felixkuebler/HomeAutomation-MotorController/Hardware/Electronics/Render/MotorController_back.png

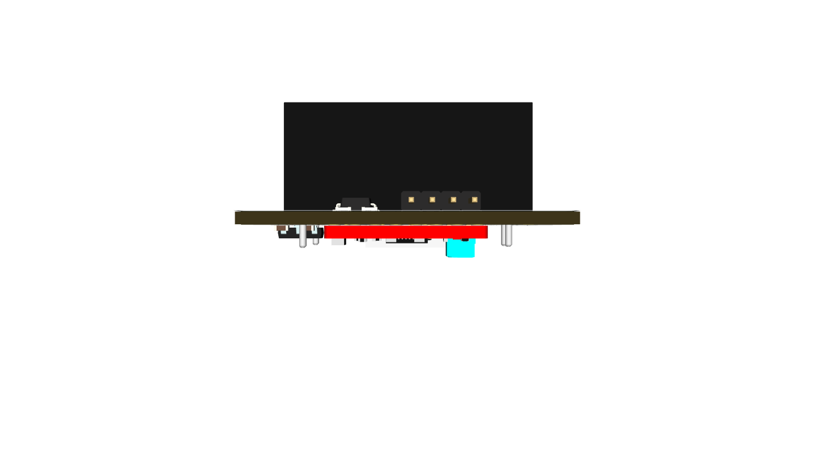
Hardware/Electronics/Render/MotorController_back.png
