felixkuebler/HomeAutomation-MotorController/Software/Source/MotorController/web_interface.h

#ifndef WEB_INTERFACE
#define WEB_INTERFACE


String generateHeader(wifi_obj wifi_info)
{
  String page="";

  page += "<header>" + wifi_info.host_name +" Settings</header>";

  return page;
}

String generateGeneralSettings(wifi_obj wifi_info)
{
  String page = "";
  
  page +="<div id=\"general\">";
    page +="<h1>General Settings</h1>";
    page +="<br>";
    page +="<div>";
      page +="Device Name ";
      page +="<input class=\"text-input\" type=\"text\" id=\"host_name\" value=\"" + wifi_info.host_name + "\">";
    page +="</div>";
    page +="<br>";
    page +="<div>";
      page +="Device Password ";
      page +="<input class=\"text-input\" type=\"text\" id=\"host_pw\" value=\"" + wifi_info.host_pw + "\">";
    page +="</div>";
    page +="<br>";
    page +="<div class=\"info\">Choose a device name to access this website from your local network (http://device-name/). If the device is not able to connect to the network a wifi hotspot with an identical name will be generated.</div>";
    page += "<br>";
    page += "<br>";
    page +="<div>";
      page +="Update Firmware";
      page +="<form class='update-form' method='POST' action='/update' enctype='multipart/form-data'>";
        page +="<input class='file-input' type='file' name='update'>";
        page +="<input class='btn-input' type='submit' value='Update'>";
      page +="</form>";
    page +="</div>";
  page +="</div>";

  return page;
}

String generateWifiSettings(wifi_obj wifi_info)
{
  String page ="";

  page += "<div class=\"hidden\" id=\"wifi\">";
    page += "<h1>WiFi Settings</h1>";
    page += "<br>";
    page += "<div>";
      page += "Network Name "; 
      page += "<select class=\"select-input\" id=\"wifi_ssid\">";
        page += "<option value=\"" + wifi_info.wifi_ssid + "\">" + wifi_info.wifi_ssid + "</option>";

        int wifiCount = WiFi.scanNetworks();
        for(int i=0; i< wifiCount; i++)
        {
          page += "<option value=\"" + WiFi.SSID(i) + "\">" + WiFi.SSID(i) + "</option>";
        }
      page += "</select>"; 
    page += "</div>";
    page += "<br>";
    page += "<div>";
      page += "Network Password ";
      page += "<input class=\"text-input\" type=\"text\" id=\"wifi_pw\" value=\"" + wifi_info.wifi_pw + "\">";
    page += "</div>";
    page += "<br>";
    page += "<div class=\"info\">Select a Network for this device to connect to. The selected Network must be password protected!</div>";
  page += "</div>";
  
  return page;
}


String generateMQTTSettings(wifi_obj wifi_info, motor_obj motor_info)
{
  String page = "";
  
  page += "<div class=\"hidden\" id=\"mqtt\">";
    page += "<h1>MQTT Settings</h1>";
    page += "<br>";
    page += "<div>";
      page += "Broker IP ";
      page += "<input class=\"text-input\" type=\"text\" id=\"mqtt_broker\" value=\"" + wifi_info.mqtt_broker + "\">";
    page += "</div>";
    page += "<br>";
    page +="<div class=\"info\">Enter the local IP of your MQTT broker (e.g. Mosquitto on a Raspbarry Pi).</div>";
    page += "<br>";
    page += "<div>";
      page += "<br>";        
      page += "<div>";
        page += "Motor Topic ";
        page += "<input class=\"text-input\" type=\"text\" id=\"motor_topic\" value=\"" + motor_info.topic + "\">";
      page += "</div>";
      page += "<br>";
      page += "<div>";
        page += "Motor Range ";
        page += "<input class=\"text-input\" type=\"text\" id=\"motor_range_extern\" value=\"" + motor_info.range_extern + "\">";
      page += "</div>";
      page += "<br>";
      page += "<div>";
        page += "<button class=\"btn-input btn-commands\" onclick=\"calibrateMotor()\">Motor Calibration</button>";      
      page += "</div>";
    page += "</div>";  
  page += "</div>";

  return page;
}

String generateOpenhabScript()
{
  String switch_id;
  String switch_name;

  String switch_mqtt_topic;

  String switch_command_on;
  String switch_command_off;
  String switch_command_toggle;

  String for_sitemap = "";
  for_sitemap += "Switch item=" + switch_id;

  String for_items = "";
  for_items += "Switch " + switch_id + "\"" + switch_name + "\"";
  for_items += "{mqtt=\"";
  for_items += ">[broker:" + switch_mqtt_topic + ":command:ON:" + switch_command_on + "],";
  for_items += ">[broker:" + switch_mqtt_topic + ":command:OFF:" + switch_command_off + "]";
  for_items += "\"}\n";
  for_items += "String mqttMessage_" + switch_id + " {mqtt=\"<[broker:" + switch_mqtt_topic + ":state:default]\"}";

  String for_rules = "";
  for_rules += "rule \"mqttMessage_" + switch_id + "_changed\n";
  for_rules += "when\n";
  for_rules += "\tItem mqttMessage_" + switch_id + " changed\n";
  for_rules += "then\n";
  for_rules += "\tif(mqttMessage_" + switch_id + ".state.toString.contains(\"" + switch_command_off + "\"))\n";
  for_rules += "\t{\n";
  for_rules += "\t\t" + switch_id + ".postUpdate(OFF)\n";
  for_rules += "\t}\n";
  for_rules += "\telse if(mqttMessage_" + switch_id + ".state.toString.contains(\"" + switch_command_on + "\"))\n";
  for_rules += "\t{\n";
  for_rules += "\t\t" + switch_id + ".postUpdate(ON)\n";
  for_rules += "\t}\n";
  for_rules += "\telse if(mqttMessage_" + switch_id + ".state.toString.contains(\"" + switch_command_toggle + "\"))\n";
  for_rules += "\t{\n";
  for_rules += "\t\t" + switch_id + ".postUpdate(if(" + switch_id + ".state == ON) OFF else ON)\n";
  for_rules += "\t\tmqttMessage_" + switch_id + ".postUpdate(\"\")\n";
  for_rules += "\t}\n";
  for_rules += "end";

  return "";
}

String generateScript()
{
  String script ="";
  
  script += "<script>";
    script += "function handleSettings(element){"; 
      script += "var setting_buttons= document.getElementsByClassName(\"btn-settings\");";
      script += "for (var i = 0; i < setting_buttons.length; ++i){";
        script += "var setting_button = setting_buttons[i]; ";
        script += "var setting_frame= document.getElementById(setting_button.getAttribute(\"for\"));";
        script += "setting_button.style.borderWidth= \"1px\";";
        script += "setting_button.style.background = \"rgba(120,120,120,0.95)\";";
        script += "setting_button.classList.remove(\"dontHover\");";
        script += "setting_frame.style.display = \"none\";";
      script += "}";
      script += "var setting_frame = document.getElementById(element.getAttribute(\"for\")); ";
      script += "setting_frame.style.display = \"block\";";
      script += "element.style.borderWidth = \"0\";";
      script += "element.style.background = \"rgba(180,180,180,0.95)\";";
      script += "element.classList.add(\"dontHover\");";
    script += "}";

     script += "function handleOptions(element){"; 
      script += "var setting_buttons= document.getElementsByClassName(\"btn-options\");";
      script += "for (var i = 0; i < setting_buttons.length; ++i){";
        script += "var setting_button = setting_buttons[i]; ";
        script += "var setting_frame= document.getElementById(setting_button.getAttribute(\"for\"));";
        script += "setting_button.style.background = \"rgba(120,120,120,0.95)\";";
        script += "setting_button.classList.remove(\"dontHover\");";
        script += "setting_frame.style.display = \"none\";";
      script += "}";
      script += "var setting_frame = document.getElementById(element.getAttribute(\"for\")); ";
      script += "setting_frame.style.display = \"block\";";
      script += "element.style.background = \"rgba(180,180,180,0.95)\";";
      script += "element.classList.add(\"dontHover\");";
    script += "}";

    script += "function sendSettings(){";
      script += "var msg = \"?\";";
      script += "var selects = document.getElementsByTagName(\"select\");";
      script += "for (var i = 0; i < selects.length; ++i){";
        script += "var id = selects[i].getAttribute(\"id\");";
        script += "var value = selects[i].value;";
        script += "msg+= id + \"=\" + value + \"&\";";
      script += "}";
      script += "var inputs = document.getElementsByTagName(\"input\");";
      script += "for (var i = 0; i < inputs.length; ++i){";
        script += "var id = inputs[i].getAttribute(\"id\");";
        script += "var value = inputs[i].value;";
        script += "msg+= id + \"=\" + value + \"&\";";
      script += "}";
      script += "msg+= \"save_settings=true\";";
      script += "if(confirm(\"The system is going to reboot after the settings are saved. Do You want to continue?\"))";
      script += "{";
        script += "var xhttp = new XMLHttpRequest();";
        script += "xhttp.onreadystatechange = function(){";
          script += "if (this.readyState == 4 && this.status == 200){}";
        script += "};";
        script += "xhttp.open(\"GET\", msg, true);";
        script += "xhttp.send();";
      script += "}";
    script += "}";

    script += "function calibrateMotor(){";
      script += "var xhttp = new XMLHttpRequest();";
      script += "xhttp.onreadystatechange = function(){";
        script += "if (this.readyState == 4 && this.status == 200){}";
      script += "};";
      script += "xhttp.open(\"GET\", \"?motor_calibration=true\", true);";
      script += "xhttp.send();";
    script += "}";
    
    script += "function sendReset(){";
      script += "if(confirm(\"The system is going to roboot after settings are reset to default. Do You want to continue?\"))";
      script += "{";
        script += "var xhttp = new XMLHttpRequest();";
        script += "xhttp.onreadystatechange = function(){";
          script += "if (this.readyState == 4 && this.status == 200){}";
        script += "};";
        script += "xhttp.open(\"GET\", \"?reset_settings=true\", true);";
        script += "xhttp.send();";
      script += "}";
    script += "}";

  script += "</script>";

  return script;
}

String generateCSS()
{
  String css = "";
  
  css += "<style>";
    css += "header {width:100vw; height:25vh; margin:0; padding:0; text-align:center; display: table-cell; vertical-align:middle; font-family:Verdana; font-weight:100; font-size:11vh; background:rgba(180,180,180,0.7)}";
    css += "h1 {margin:0; padding:0; font-family:Verdana; font-weight:100; font-size:6vh}";
    css += "button:focus {outline:0}";
    css += ".main-frame {width:100vw; height:75vh; margin:0; padding:0; overflow:hidden}";
    css += ".left-frame {width:20vw; height:75vh; float:left; margin:0; padding:0; text-align:center; position:relative; font-family:Verdana; font-weight:100; font-size:4vh}";
    css += ".right-frame {width:80vw; height:75vh; float:right; margin:0; padding:0; text-align:center; position:relative; font-family:Verdana; font-weight:100; font-size:3vh; background:rgba(180,180,180,0.95)}";
    css += ".scrollable {overflow:scroll; width:80vw; height:55vh; position:absolute; bottom:0}";
    css += ".spaceholder {width:20vw; height:31.1vh; margin:0; margin-top:30vh; padding:0; text-align:center; font-family:Verdana; font-weight:100; font-size:3vh; background:rgba(120,120,120,0.95)}";
    css += ".info {width:40vw; margin-left: 20vw; font-family:Verdana; font-weight:100; font-size:1.8vh}";
    css += ".hidden {display:none}";
    css += ".btn {background:rgba(120,120,120,0.95); width:20vw; border:none; text-align:center; text-decoration:none; cursor:pointer; margin:0; padding:0; font-family:Verdana; font-weight:100; border-style: solid; border-color:rgba(110,110,110,0.95); border-width:1px;}";
    css += ".btn:not(.dontHover):hover {background:rgba(100,100,100,0.95) !important}";
    css += ".selected {background:rgba(180,180,180,0.95); border-width:1;}";
    css += ".selected-noborder {background:rgba(180,180,180,0.95); border-width:0;}";
    css += ".btn-settings {height:10vh; font-size:3vh}";
    css += ".btn-requests {height:7vh; font-size:2vh}";
    css += ".settings {position:absolute; top:0}";
    css += ".requests {position:absolute; bottom:0}";
    css += ".btn-options {max-width:10vw; height:4vh; font-size:2vh; display:inline-block}";
    css += ".btn-commands {max-width:20vw; height:4vh; font-size:2vh}";
    css += ".text-input {width:20vw; height:3vh; margin:0; padding:0; font-family:Verdana; font-weight:100; font-size:2vh}";
    css += ".file-input {width:20vw; height:4vh; margin:0; padding:0; font-family:Verdana; font-weight:100; font-size:2vh; accept=\"*.ino.bin\"}";
    css += ".btn-input {width:20vw; height:4vh; margin:0; padding:0; font-family:Verdana; font-weight:100; font-size:2vh}";
    css += ".select-input {width:20vw; height:4vh; margin:0; padding:0; font-family:Verdana; font-weight:100; font-size:2vh}";
    css += "body {margin:0; padding:0; overflow:hidden; background-image:url('data:image/jpeg;base64,";
    //String str ="url('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')";
    css += "'); background-size: cover; background-repeat: no-repeat;}";
  css += "</style>";

  return css;
}

String generateWebpage(wifi_obj wifi_info, motor_obj motor_info)
{
  String page = "";
  
  page += "<!DOCTYPE html>";
    page += "<body>";
 
      page += generateHeader(wifi_info);

      page += "<div class=\"main-frame\">";
        page += "<div class=\"left-frame\">";
          page += "<div class=\"settings\">";
            page += "<button class=\"btn btn-settings selected-noborder dontHover\" for=\"general\" onclick=\"handleSettings(this)\">Gerneral Settings</button>";
            page += "<button class=\"btn btn-settings\" for=\"wifi\" onclick=\"handleSettings(this)\">WiFi Settings</button>";
            page += "<button class=\"btn btn-settings\" for=\"mqtt\" onclick=\"handleSettings(this)\">MQTT Settings</button>";
          page += "</div>";
          page += "<div class=\"spaceholder\"></div>";
          page += "<div class=\"requests\">";
            page += "<button class=\"btn btn-requests\" onclick=\"sendSettings()\">Save Settings</button>";
            page += "<button class=\"btn btn-requests\" onclick=\"sendReset()\">Reset Settings</button>"; 
          page += "</div>";
        page += "</div>";
        page += "<div class=\"right-frame\">";

          page += generateGeneralSettings(wifi_info);
          page += generateWifiSettings(wifi_info);
          page += generateMQTTSettings(wifi_info, motor_info);

        page += "</div>";
      page += "</div>";

      page += generateScript();
      page += generateCSS();

    page += "</body>";
  page += "</html>";

  return page;
   
}


#endif //WEB_INTERFACE

 
